tom01h/usb-ospi/firm/Core/Inc/main.h

#define LINEAR_BURST_READ 0x2
#define LINEAR_BURST_WRITE 0xA
#define DUMMY_CLOCK_CYCLES_SRAM_READ 2
#define DUMMY_CLOCK_CYCLES_SRAM_WRITE 0
#define BUFFERSIZE 512
